Bongorian/M5basspiezohat/firmware/components/bass_core/include/decimator_coefficients.hpp

#pragma once
#include <array>
namespace bass {
// 63-tap Hamming FIR: 900 Hz cutoff at 16 kHz, unity DC gain.
inline constexpr std::array<float, 63> kDecimatorFir{
    -8.2156171377e-04f,
    -8.0808653300e-04f,
    -7.2135996753e-04f,
    -5.2223901129e-04f,
    -1.6266005680e-04f,
    3.9419374672e-04f,
    1.1501708762e-03f,
    2.0509793037e-03f,
    2.9740679150e-03f,
    3.7310265958e-03f,
    4.0875691175e-03f,
    3.8007648000e-03f,
    2.6693884385e-03f,
    5.8979317029e-04f,
    -2.3926952570e-03f,
    -6.0476295373e-03f,
    -9.9481118964e-03f,
    -1.3490738987e-02f,
    -1.5948614691e-02f,
    -1.6553729848e-02f,
    -1.4599584399e-02f,
    -9.5505336509e-03f,
    -1.1418170241e-03f,
    1.0545858349e-02f,
    2.5050775331e-02f,
    4.1542410143e-02f,
    5.8883502104e-02f,
    7.5736817345e-02f,
    9.0704571432e-02f,
    1.0248315413e-01f,
    1.1001291217e-01f,
    1.1260281522e-01f,
    1.1001291217e-01f,
    1.0248315413e-01f,
    9.0704571432e-02f,
    7.5736817345e-02f,
    5.8883502104e-02f,
    4.1542410143e-02f,
    2.5050775331e-02f,
    1.0545858349e-02f,
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
};
}
